qubixal/qbMX/prod-3d-models/top-cover.stl

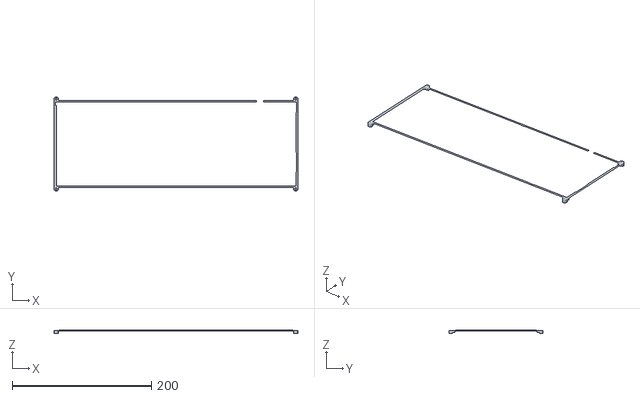
[picture p19: CAD file, 2026-08-24]
prod-3d-models/top-cover.stl
350.0 x 135.5 x 5.00
