qubixal/qbMX/128x32-OLED.STEP

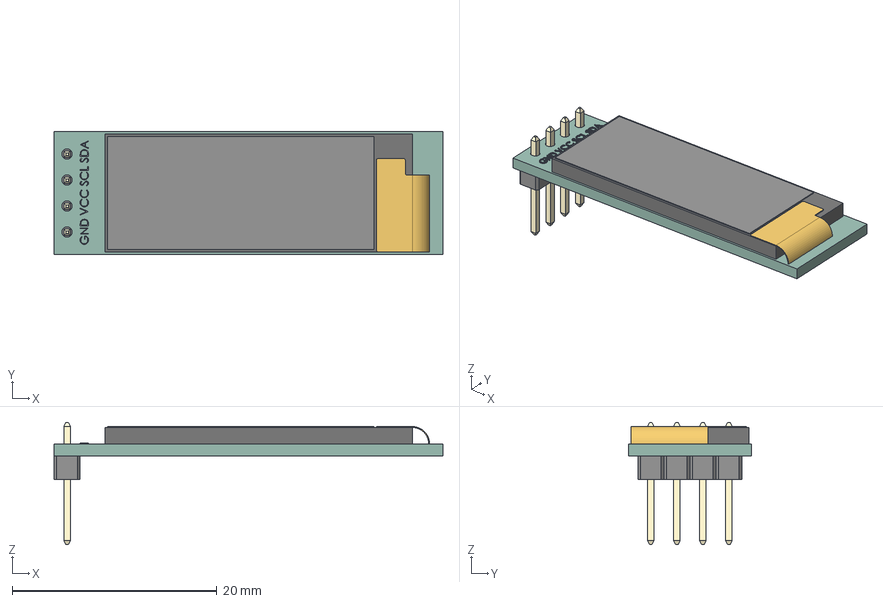
[picture p20: CAD file, 2026-08-21]
128x32-OLED.STEP
38.0 x 12.0 x 11.9 mm
