qubixal/qbMX/dsa-keycap-master/DSA 1.75u.step

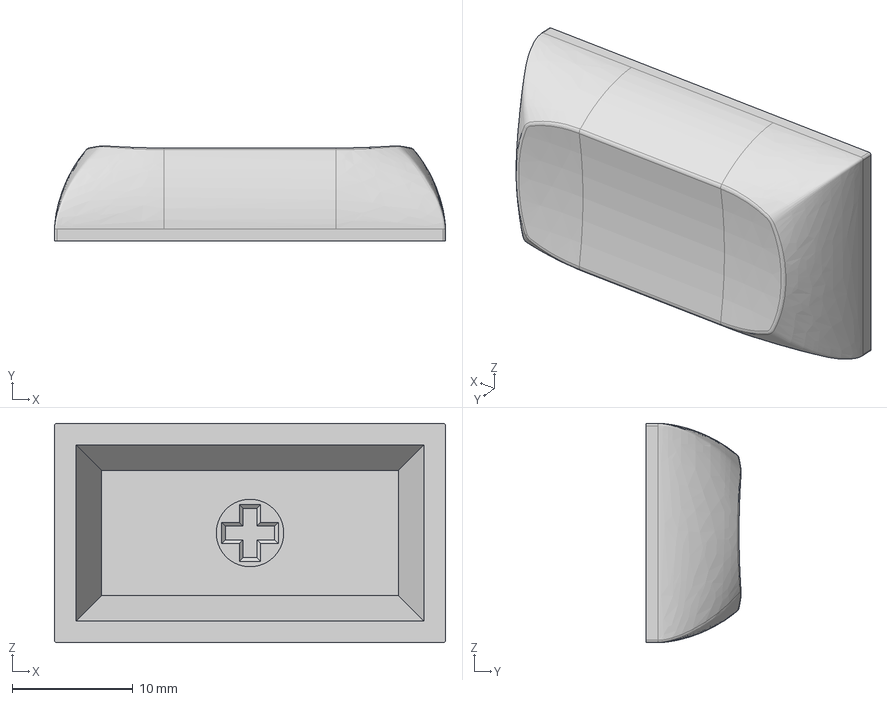
[picture p21: CAD file, 2026-08-21]
dsa-keycap-master/DSA 1.75u.step
32.5 x 7.91 x 18.2 mm
