qubixal/qbMX/prod-3d-models/knob.stl

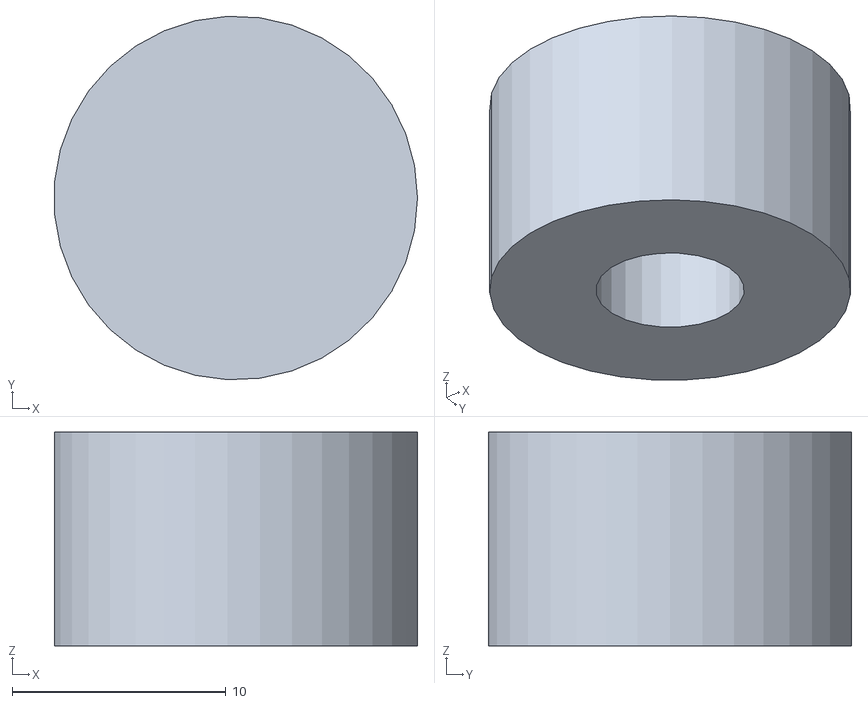
[picture p22: CAD file, 2026-08-24]
prod-3d-models/knob.stl
17.0 x 17.0 x 10.00
