qubixal/qbMX/prod-3d-models/acrylic-cover.stl

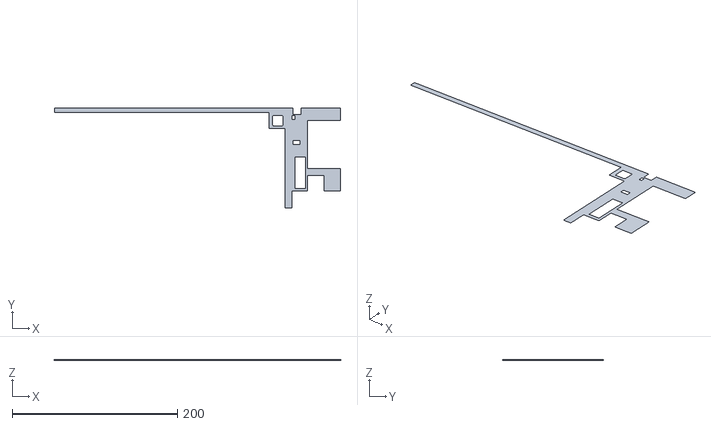
[picture p23: CAD file, 2026-08-24]
prod-3d-models/acrylic-cover.stl
346.0 x 121.0 x 0.5
